hello-robot/stretch_tool_share/tool_share/stretch_RE1_arm/README.md

## Stretch RE1 Arm Model

**Created by**: Hello Robot Inc

This is an STL model of the Stretch RE1 arm (retracted) including the end-of-arm interface. It can assist the design of your own tools for your Stretch. 



| Files                                          |
| ---------------------------------------------- |
| [Stretch_RE1_Arm.STL](CAD/Stretch_RE1_Arm.STL) |
