hello-robot/stretch_tool_share/tool_share/adapted_spoon_V1/images/Spoon.jpeg

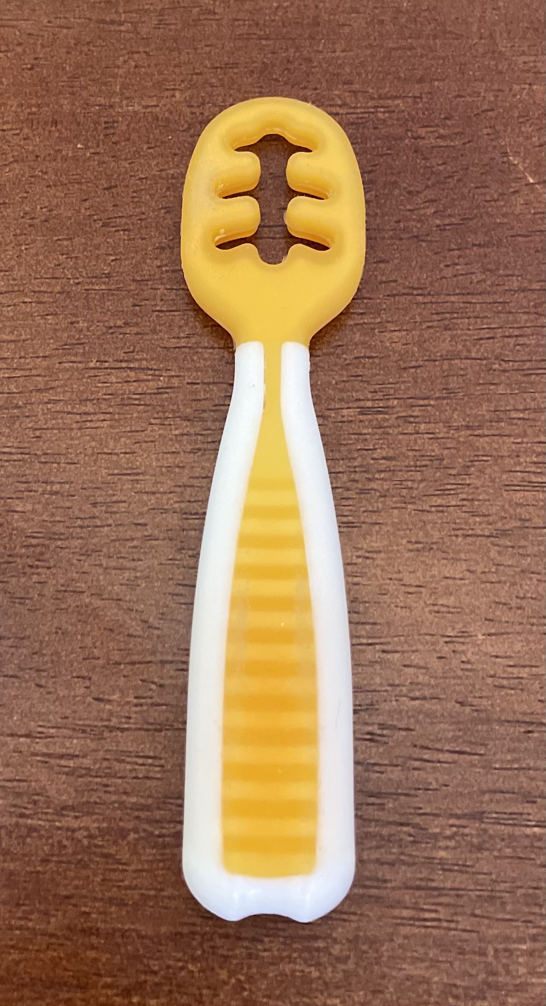
tool_share/adapted_spoon_V1/images/Spoon.jpeg
