hello-robot/stretch_tool_share/tool_share/phone_holder_V1/images/iPhone_Mount_Amazon.PNG

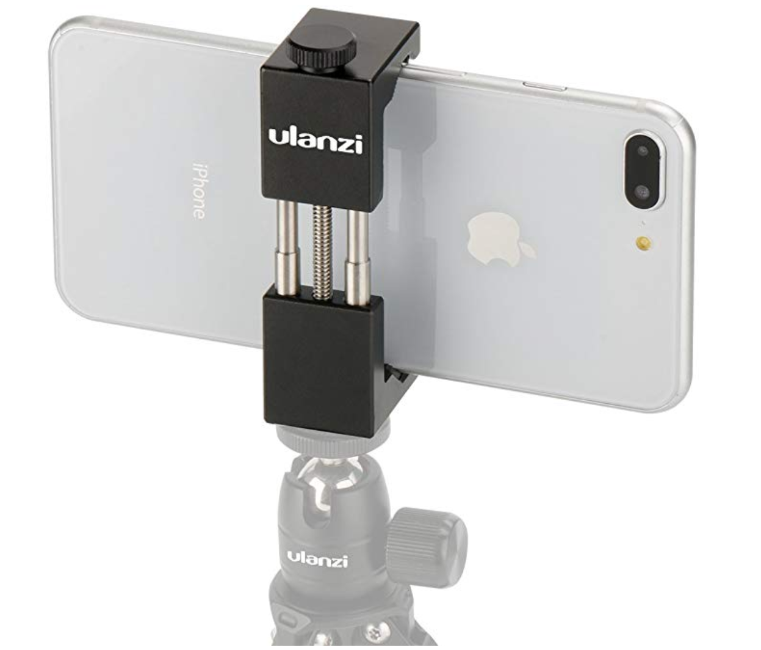
tool_share/phone_holder_V1/images/iPhone_Mount_Amazon.PNG
