hello-robot/stretch_tool_share/tool_share/stretch_teleop_kit/images/camera_view_A.jpg

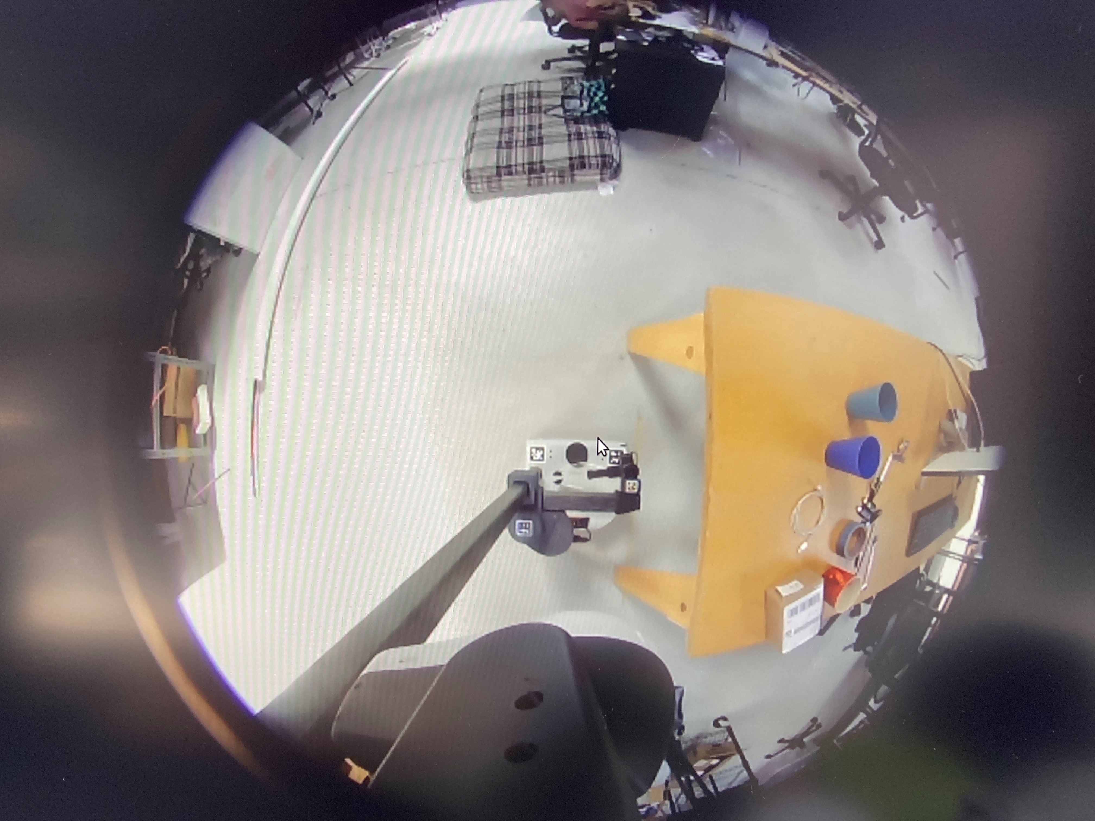
tool_share/stretch_teleop_kit/images/camera_view_A.jpg
