hello-robot/stretch_tool_share/tool_share/stretch_teleop_kit/images/head_camera_A.png

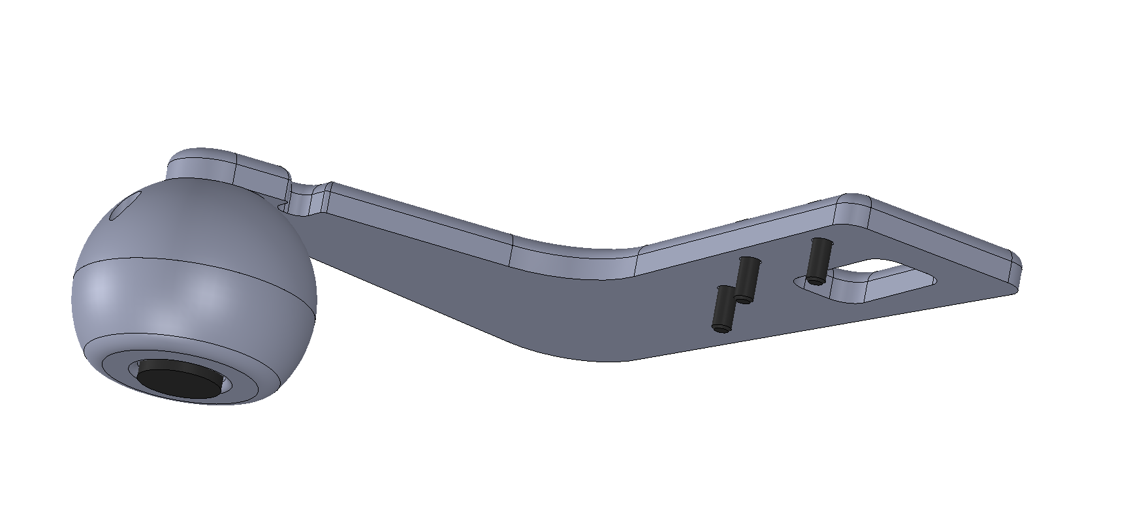
tool_share/stretch_teleop_kit/images/head_camera_A.png
