hello-robot/stretch_tool_share/tool_share/stretch_teleop_kit/images/wrist_camera_C.png

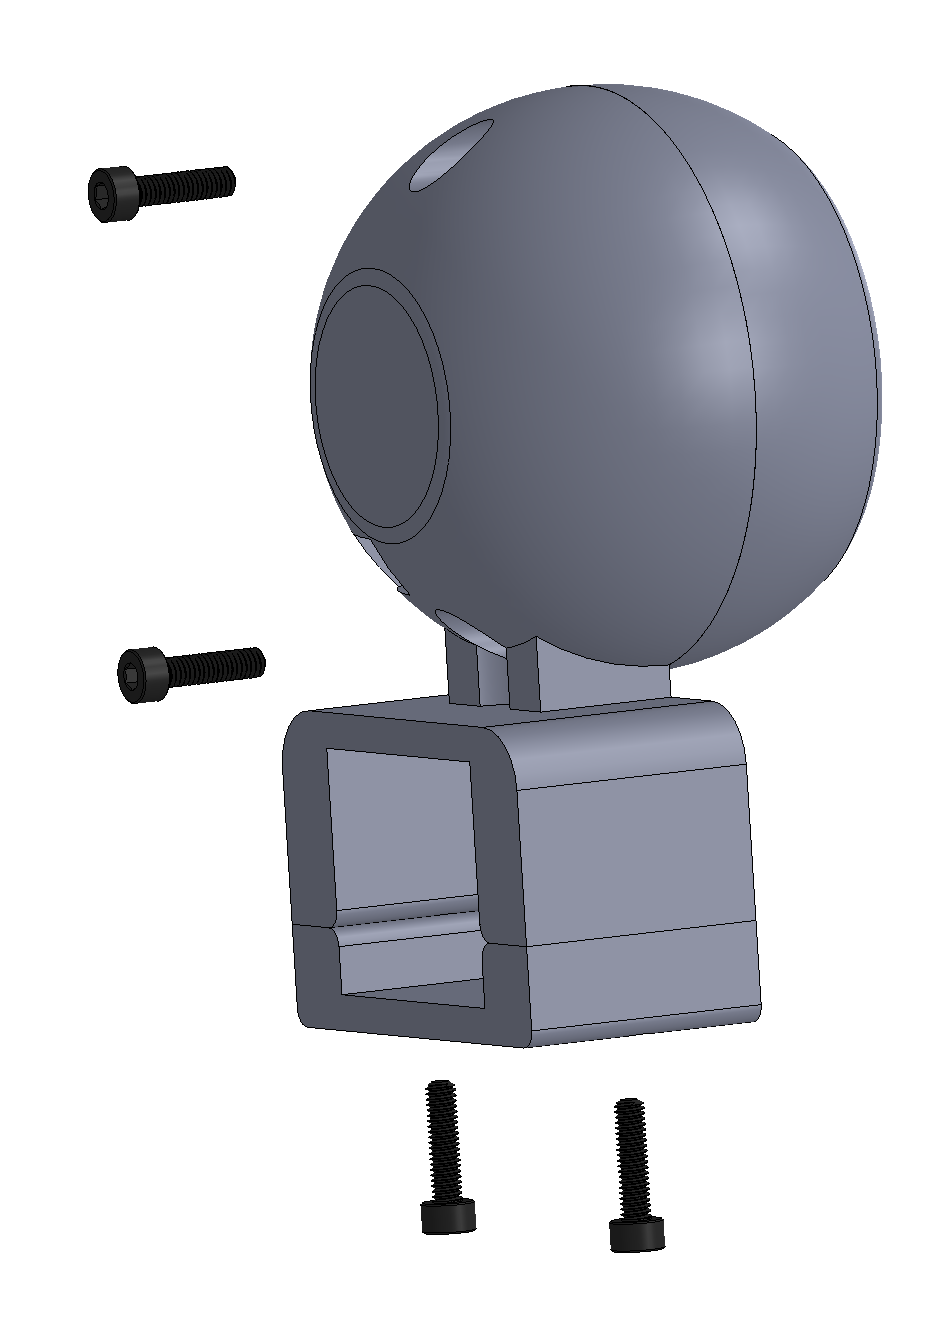
tool_share/stretch_teleop_kit/images/wrist_camera_C.png
