hello-robot/stretch_tool_share/tool_share/swivel_tablet_mount/images/Capture.PNG

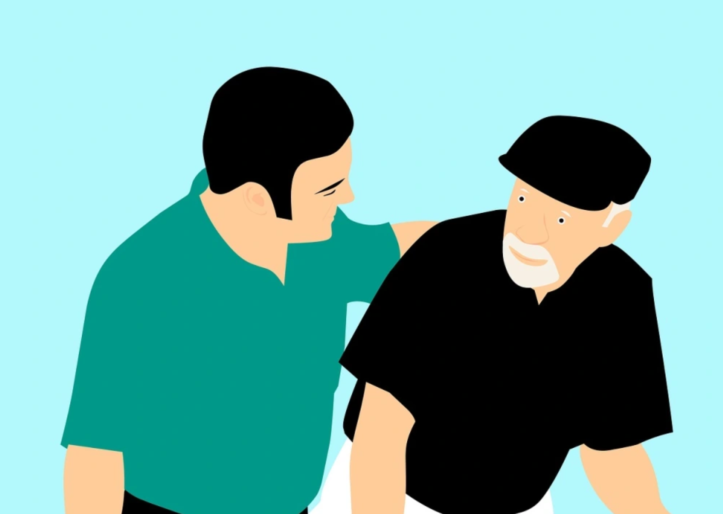
tool_share/swivel_tablet_mount/images/Capture.PNG
