hello-robot/stretch_tool_share/tool_share/stretch_dex_wrist/stretch_description/meshes/link_wrist_roll.STL

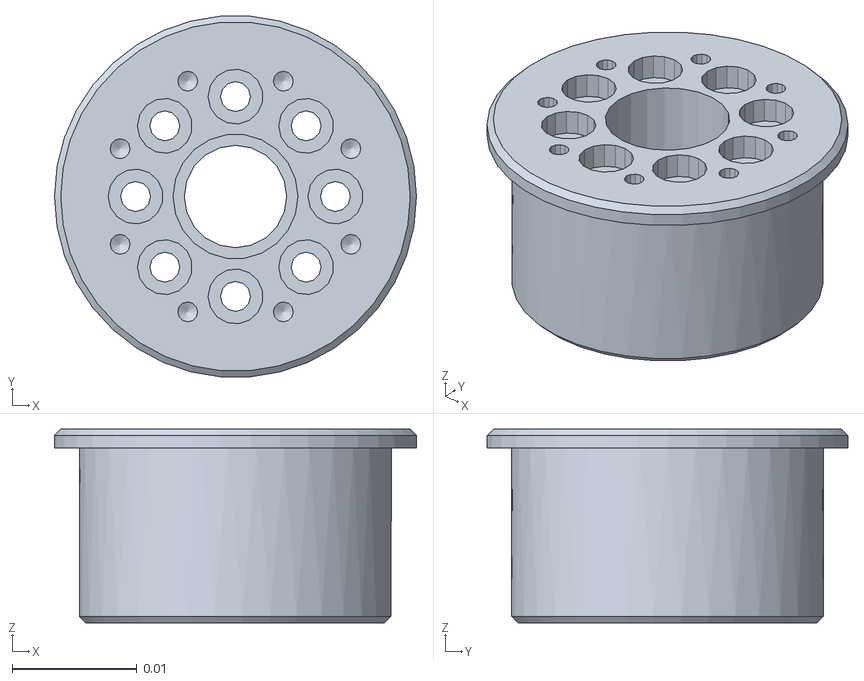
[picture p100: CAD file, 2021-03-02]
tool_share/stretch_dex_wrist/stretch_description/meshes/link_wrist_roll.STL
0.029 x 0.0289 x 0.0155
