hello-robot/stretch_tool_share/tool_share/stretch_docking_station/stretch_docking_station_description/meshes/link_docking_aruco.STL

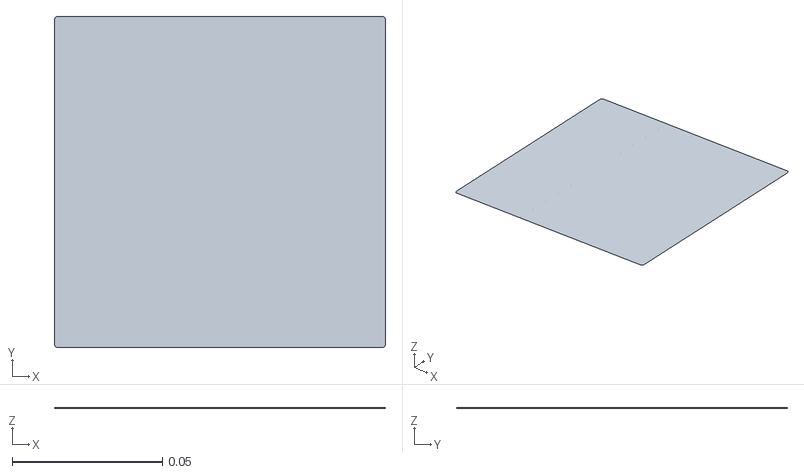
[picture p101: CAD file, 2022-05-09]
tool_share/stretch_docking_station/stretch_docking_station_description/meshes/link_docking_aruco.STL
0.11 x 0.11 x 0.00025
