hello-robot/stretch_tool_share/tool_share/stretch_RE1_arm/CAD/Hello-Robot-Stretch-RE1_Wrist_Module.STEP

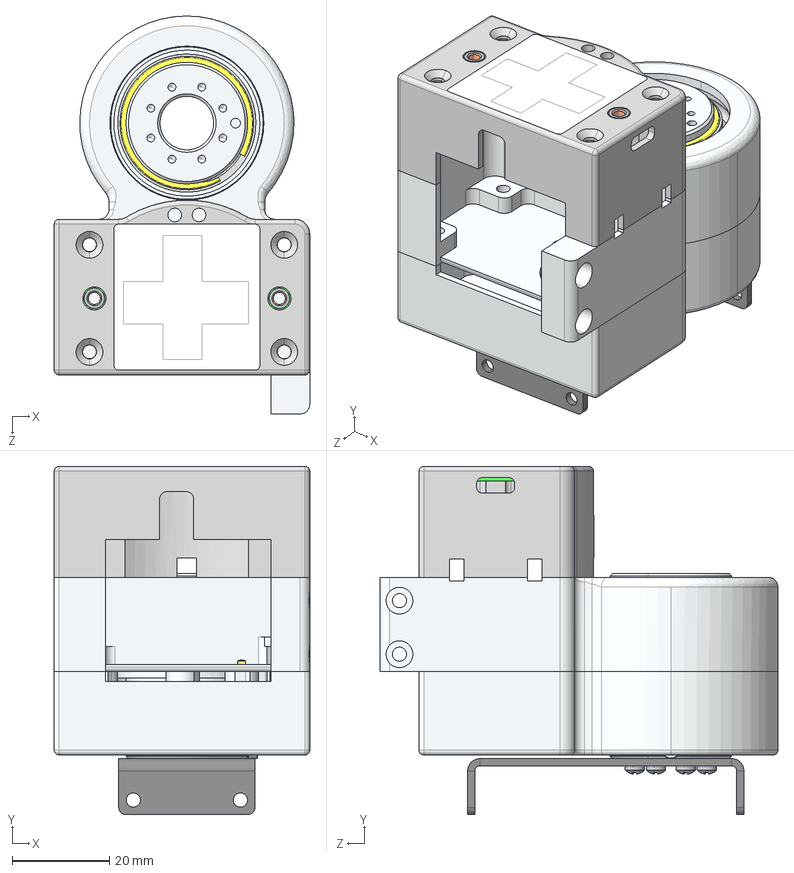
[picture p102: CAD file, 2021-01-28]
tool_share/stretch_RE1_arm/CAD/Hello-Robot-Stretch-RE1_Wrist_Module.STEP
52.5 x 71.5 x 81.8 mm
HDW-609_wrist_output_shaft
HDW-207_91290A012_M2x5mm_SHCS_91290A012
BIG-608_wrist_bearing_block
3DP-239_wrist_bearing_spacer
HDW-209_25x37x7mm_BEARING_5972K216 x 2
VND-278_wrist_top_plate
VND-279_SO-M3-3ZI-PennEngineering x 2
BIG-235_wrist_top_shell
BIG-234_wrist_bottom_shell
HDW-213_94540A360_1in_SPIRAL EXTERNAL RETAINING RING_94540A360
HDW-360_Aruco_E_30x30mm
HDW-359_Aruco_D_30x30mm
HDW-607_gripper_mount_bracket
HDW-362_95836A109_M2x6mm_BHCS_Philips_95836A109 x 8
