hello-robot/stretch_tool_share/tool_share/stretch_RE1_head/CAD/Stretch_RE1_Head_Right.STL

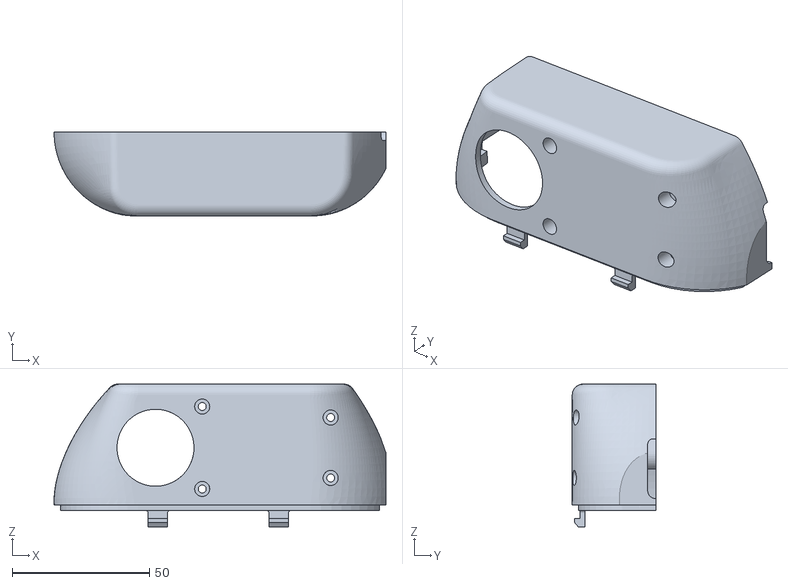
[picture p103: CAD file, 2020-10-14]
tool_share/stretch_RE1_head/CAD/Stretch_RE1_Head_Right.STL
120.8 x 30.5 x 52.0
