hello-robot/stretch_tool_share/tool_share/stretch_shoulder/Shoulder_Mount_CAD.stp

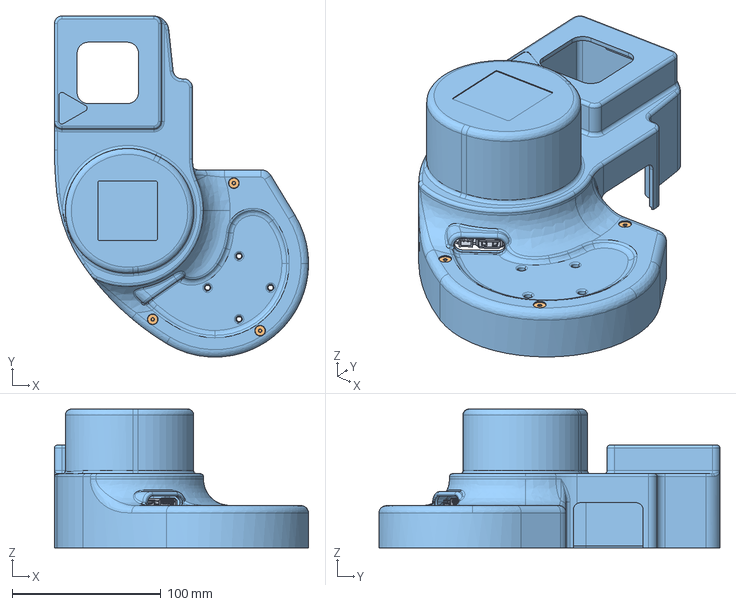
[picture p104: CAD file, 2025-03-24]
tool_share/stretch_shoulder/Shoulder_Mount_CAD.stp
171.0 x 229.5 x 93.5 mm
