hello-robot/stretch_tool_share/tool_share/stretch_teleop_kit/CAD/3DP-809_Head_Teleop_Mount_Back.STL

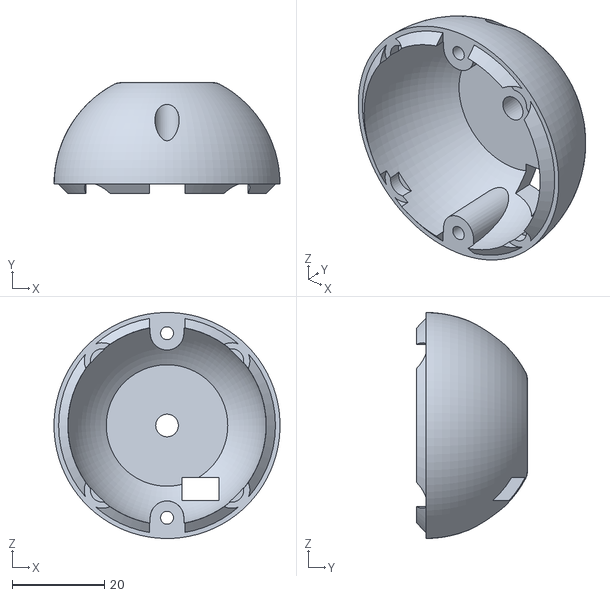
[picture p105: CAD file, 2022-04-29]
tool_share/stretch_teleop_kit/CAD/3DP-809_Head_Teleop_Mount_Back.STL
49.0 x 24.0 x 49.0
