hello-robot/stretch_tool_share/tool_share/stretch_teleop_kit/stretch_description/meshes/link_head_teleop_mount.STL

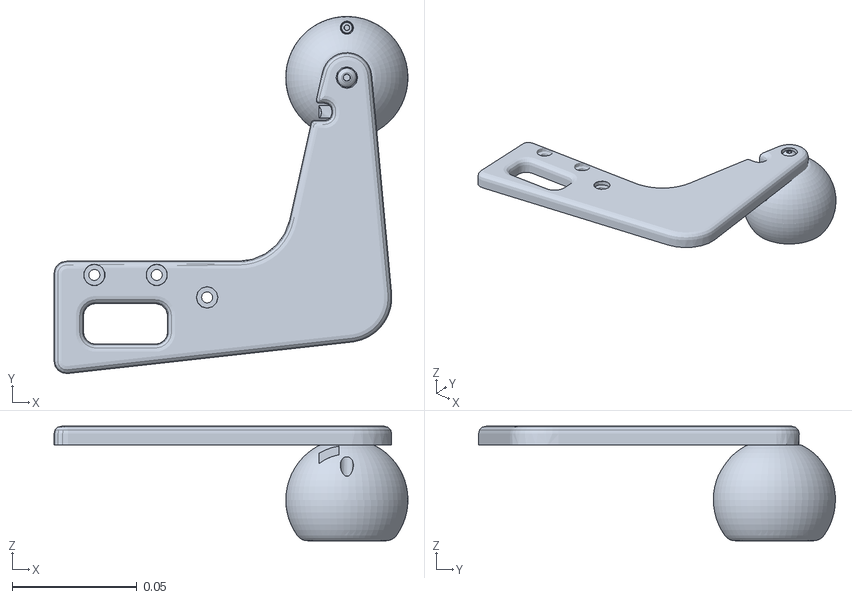
[picture p106: CAD file, 2022-04-28]
tool_share/stretch_teleop_kit/stretch_description/meshes/link_head_teleop_mount.STL
0.142 x 0.143 x 0.0459
