hello-robot/stretch_tool_share/tool_share/swiffer_mount_V1/CAD/swiffer_mount.STL

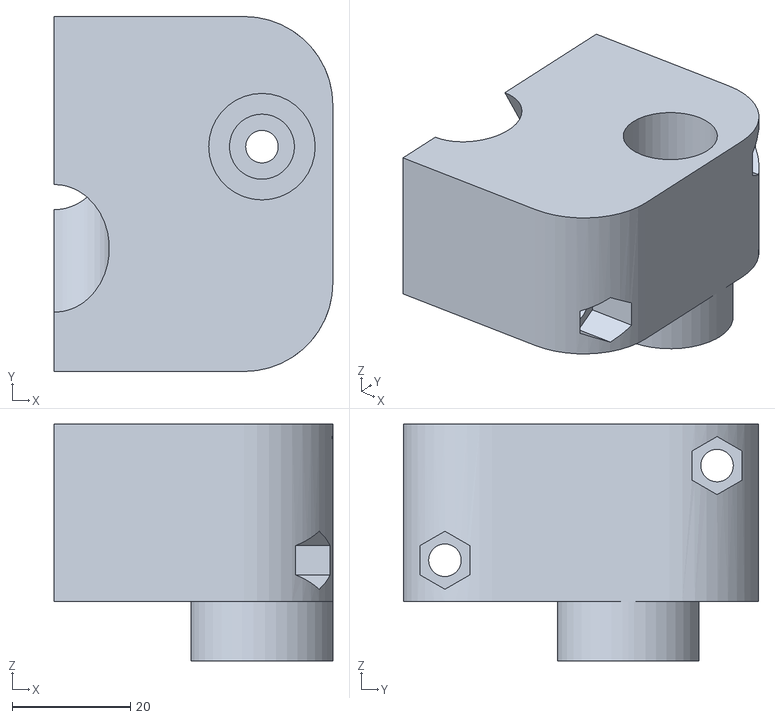
[picture p107: CAD file, 2020-06-18]
tool_share/swiffer_mount_V1/CAD/swiffer_mount.STL
47.1 x 60.0 x 40.0
