hello-robot/stretch_tool_share/tool_share/swivel_tablet_mount/CAD/swivel_adapter_top.STL

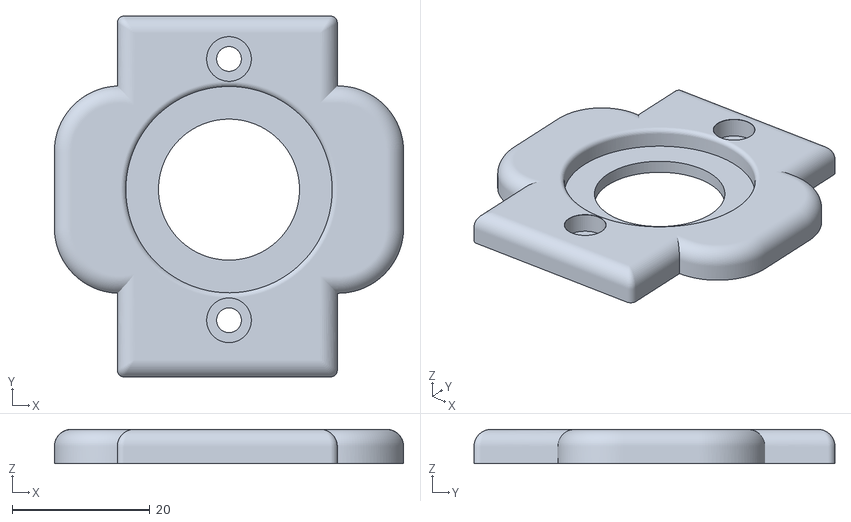
[picture p108: CAD file, 2023-11-14]
tool_share/swivel_tablet_mount/CAD/swivel_adapter_top.STL
50.8 x 52.5 x 5.00
