hello-robot/stretch_tool_share/tool_share/tray_cup_holder_V1/CAD/ASSEM_tray_cupholder_V1.STL

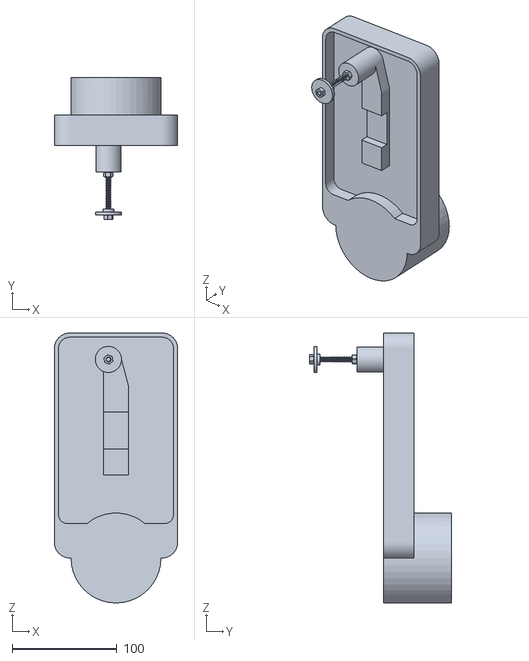
[picture p109: CAD file, 2020-06-18]
tool_share/tray_cup_holder_V1/CAD/ASSEM_tray_cupholder_V1.STL
118.0 x 136.2 x 258.0
