hello-robot/stretch_tool_share/tool_share/wrist_USB_board_camera/CAD/Board_Camera_Ball_Cover.STL

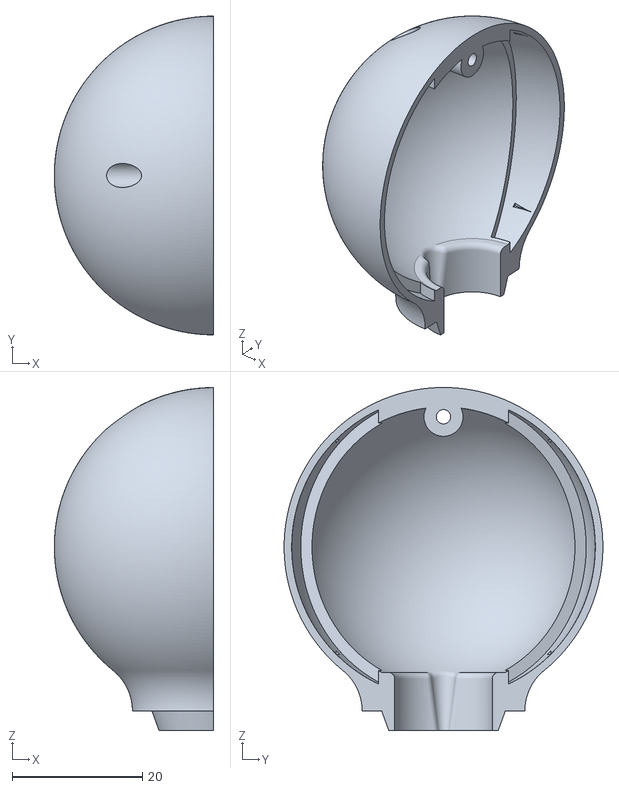
[picture p110: CAD file, 2023-03-30]
tool_share/wrist_USB_board_camera/CAD/Board_Camera_Ball_Cover.STL
24.5 x 49.0 x 52.7
