hello-robot/stretch_tool_share/tool_share/wrist_USB_board_camera/stretch_description/meshes/link_wrist_USB_board_camera.STL

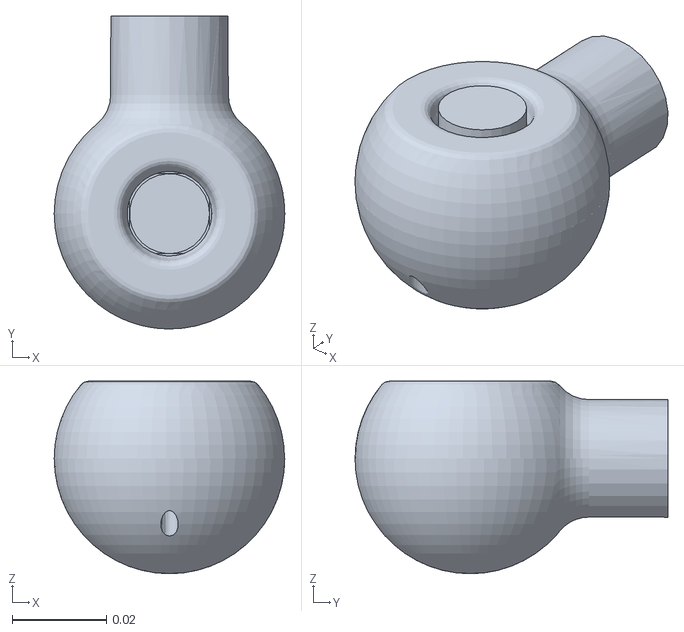
[picture p111: CAD file, 2021-02-11]
tool_share/wrist_USB_board_camera/stretch_description/meshes/link_wrist_USB_board_camera.STL
0.049 x 0.0665 x 0.0409
