hello-robot/stretch_tool_share/tool_share_SE3/eoa_wrist_dw3_tool_tablet_12in/CAD/DW3_tablet_holder.STEP

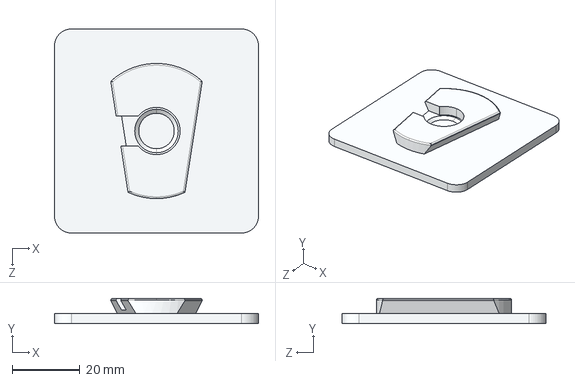
[picture p112: CAD file, 2024-01-28]
tool_share_SE3/eoa_wrist_dw3_tool_tablet_12in/CAD/DW3_tablet_holder.STEP
60.3 x 7.40 x 60.3 mm
