hello-robot/stretch_tool_share/tool_share_SE3/eoa_wrist_dw3_tool_tablet_12in/meshes/link_DW3_tablet_12in.STL

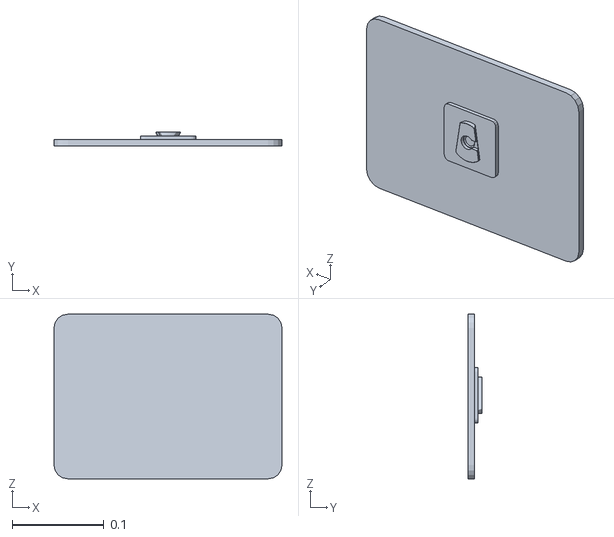
[picture p113: CAD file, 2024-01-28]
tool_share_SE3/eoa_wrist_dw3_tool_tablet_12in/meshes/link_DW3_tablet_12in.STL
0.249 x 0.0152 x 0.179
