hello-robot/stretch_tool_share/tool_share/card_holder_V1.5/CAD/base_v2.STL

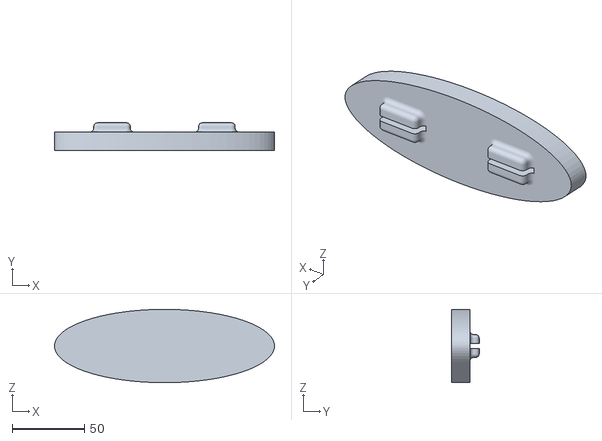
[picture p114: CAD file, 2022-08-03]
tool_share/card_holder_V1.5/CAD/base_v2.STL
152.4 x 19.1 x 50.8
