hello-robot/stretch_tool_share/tool_share/dry_erase_holder_V1/CAD/dry_erase_bushing_block.STL

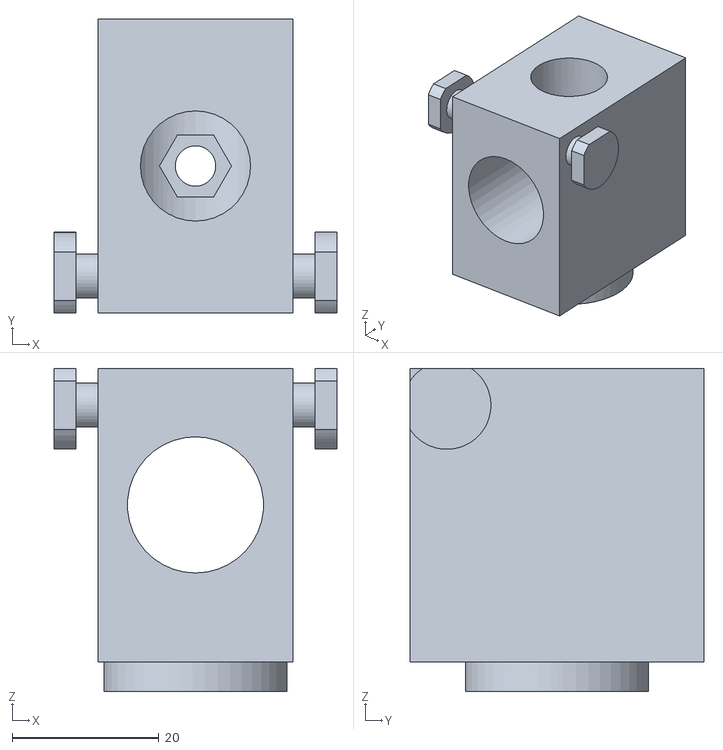
[picture p115: CAD file, 2020-06-18]
tool_share/dry_erase_holder_V1/CAD/dry_erase_bushing_block.STL
38.5 x 40.0 x 44.0
