hello-robot/stretch_tool_share/tool_share/dry_erase_holder_V1/stretch_description/meshes/link_dry_erase_marker.STL

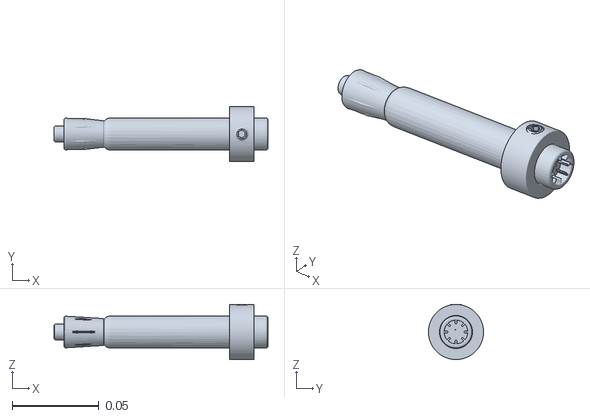
[picture p116: CAD file, 2021-02-11]
tool_share/dry_erase_holder_V1/stretch_description/meshes/link_dry_erase_marker.STL
0.123 x 0.0317 x 0.0318
