hello-robot/stretch_tool_share/tool_share/puller_v1/CAD/Puller_V1.STL

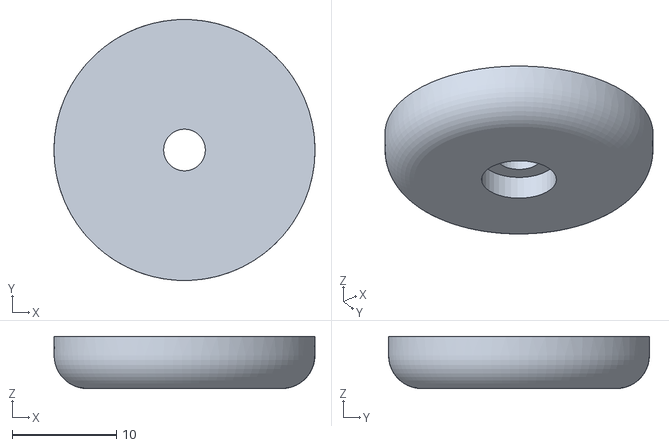
[picture p117: CAD file, 2020-06-18]
tool_share/puller_v1/CAD/Puller_V1.STL
25.0 x 25.0 x 5.00
