hello-robot/stretch_tool_share/tool_share/stretch_2_STEP/CAD/SIM-401_Roll_Hanger_simple.STEP

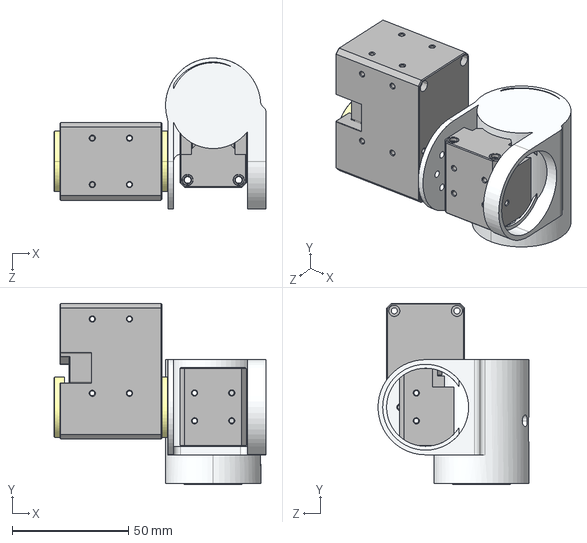
[picture p118: CAD file, 2023-01-04]
tool_share/stretch_2_STEP/CAD/SIM-401_Roll_Hanger_simple.STEP
91.3 x 78.1 x 65.0 mm
