hello-robot/stretch_tool_share/tool_share/stretch_dex_wrist/stretch_description/meshes/link_wrist_pitch.STL

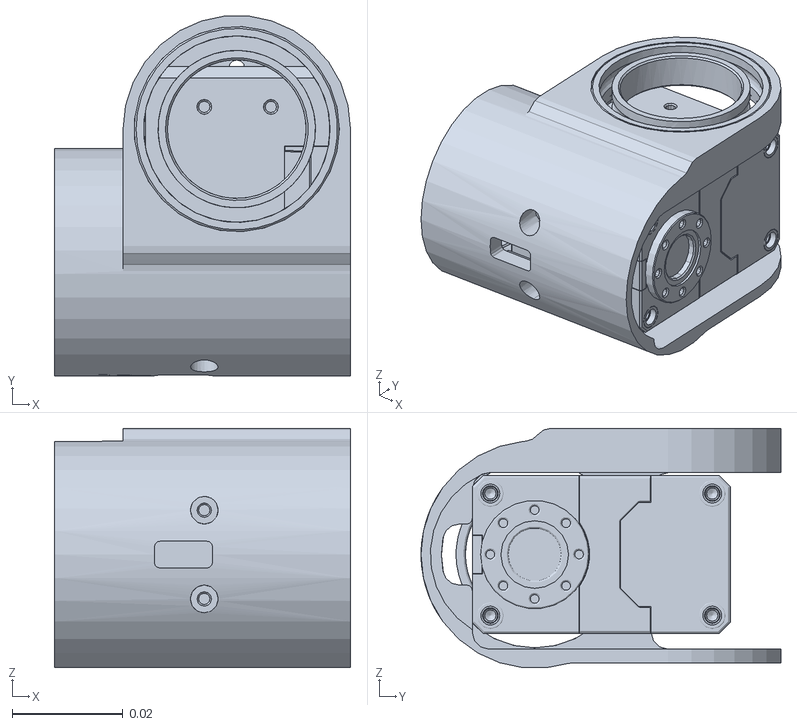
[picture p119: CAD file, 2021-02-24]
tool_share/stretch_dex_wrist/stretch_description/meshes/link_wrist_pitch.STL
0.0534 x 0.0649 x 0.0431
