hello-robot/stretch_tool_share/tool_share/stretch_RE1_arm/CAD/Stretch_RE1_Arm.STL

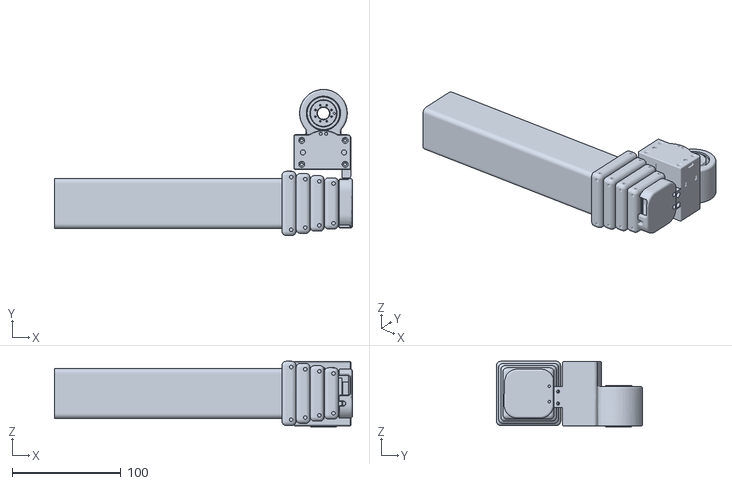
[picture p120: CAD file, 2020-06-18]
tool_share/stretch_RE1_arm/CAD/Stretch_RE1_Arm.STL
274.5 x 134.6 x 60.4
