hello-robot/stretch_tool_share/tool_share/stretch_teleop_kit/CAD/3DP-808_Teleop_Camera_Mount_Front.STL

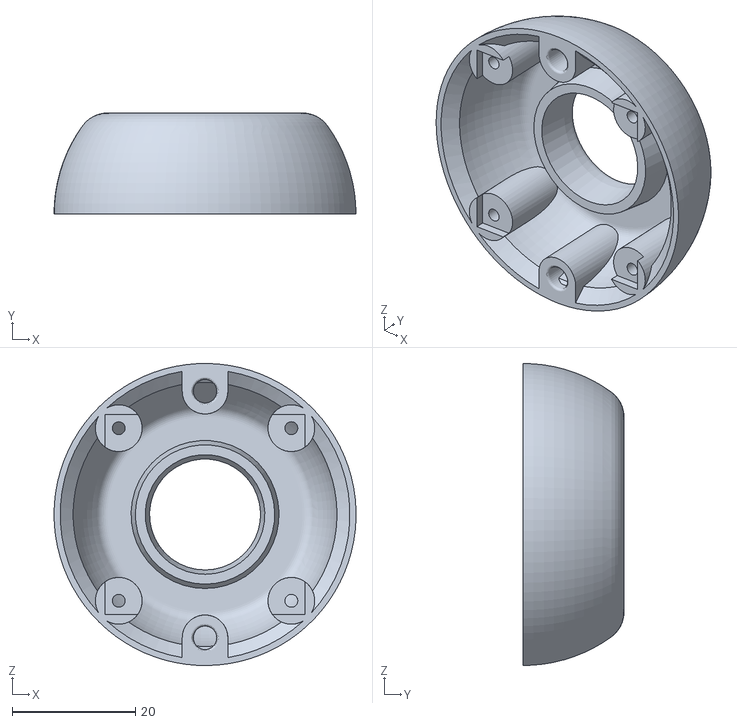
[picture p121: CAD file, 2022-04-29]
tool_share/stretch_teleop_kit/CAD/3DP-808_Teleop_Camera_Mount_Front.STL
49.0 x 16.4 x 49.0
