hello-robot/stretch_tool_share/tool_share/stretch_teleop_kit/stretch_description/meshes/link_head_teleop_camera.STL

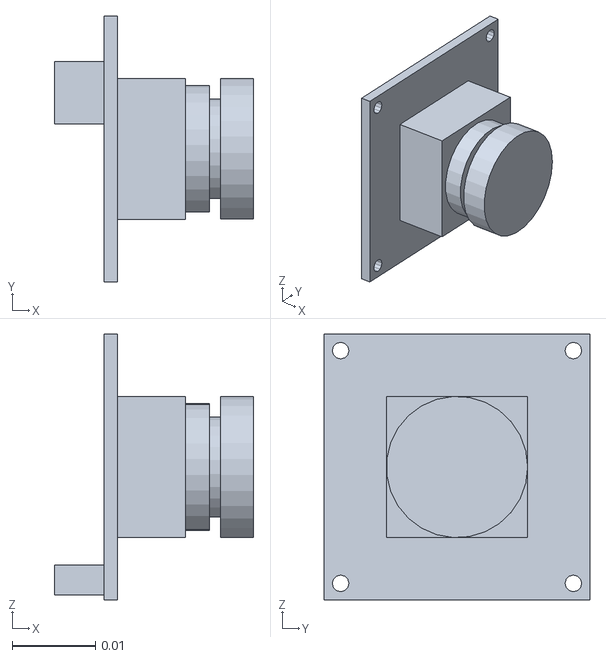
[picture p122: CAD file, 2022-04-28]
tool_share/stretch_teleop_kit/stretch_description/meshes/link_head_teleop_camera.STL
0.024 x 0.032 x 0.032
