hello-robot/stretch_tool_share/tool_share/swiffer_mount_V1/CAD/swiffer_mount_clamp.STL

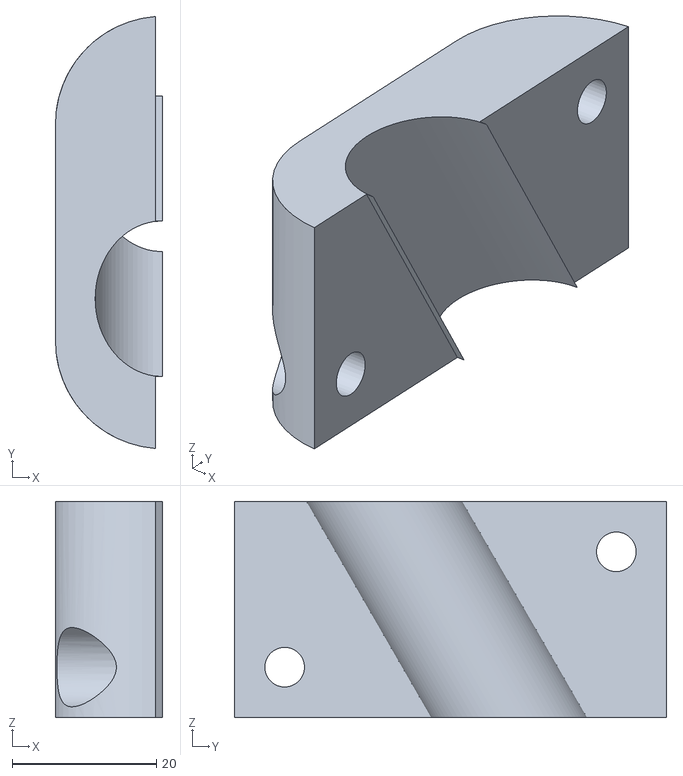
[picture p123: CAD file, 2020-06-18]
tool_share/swiffer_mount_V1/CAD/swiffer_mount_clamp.STL
14.9 x 59.9 x 30.0
