hello-robot/stretch_tool_share/tool_share/wrist_USB_board_camera/CAD/Spinel_camera_wide_fov.STL

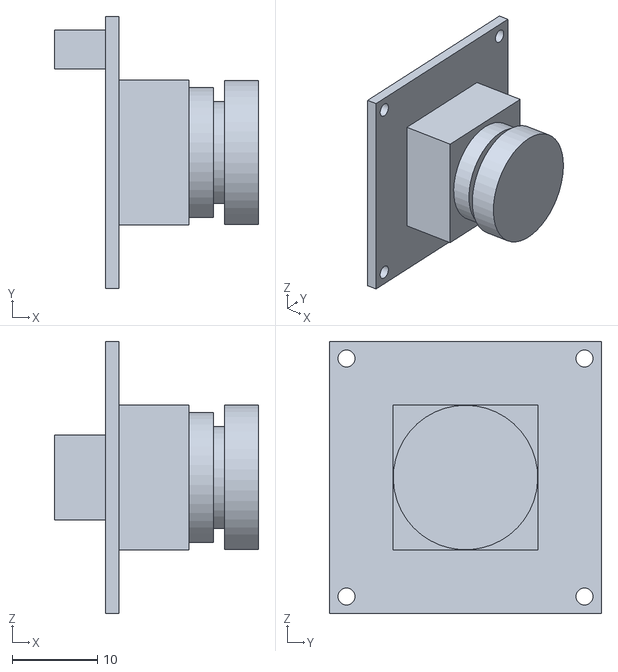
[picture p125: CAD file, 2021-02-11]
tool_share/wrist_USB_board_camera/CAD/Spinel_camera_wide_fov.STL
24.0 x 32.0 x 32.0
