hello-robot/stretch_tool_share/tool_share_SE3/eoa_wrist_dw3_tool_tablet_12in/meshes/link_DW3_tablet_12in_collision.STL

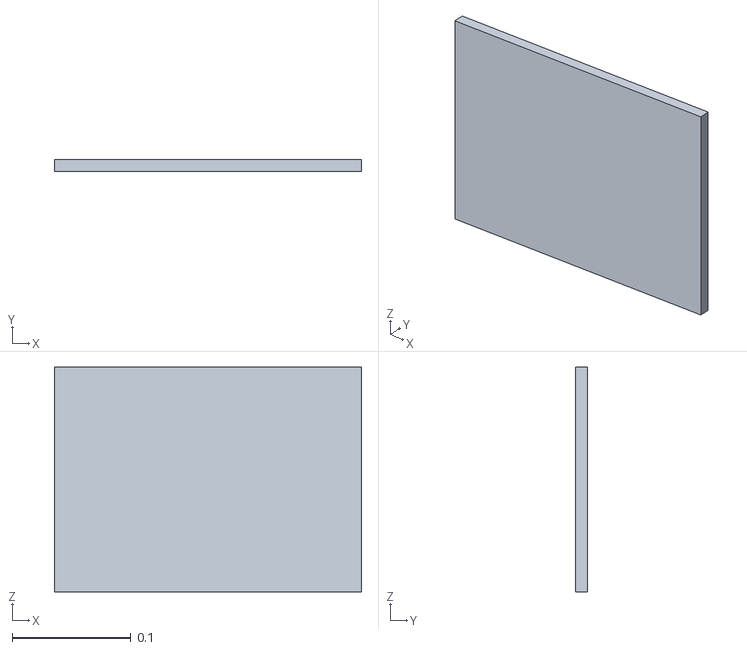
[picture p126: CAD file, 2024-01-28]
tool_share_SE3/eoa_wrist_dw3_tool_tablet_12in/meshes/link_DW3_tablet_12in_collision.STL
0.259 x 0.01 x 0.19
