hello-robot/stretch_tool_share/tool_share/card_holder_V1.5/CAD/pull_tab.STL

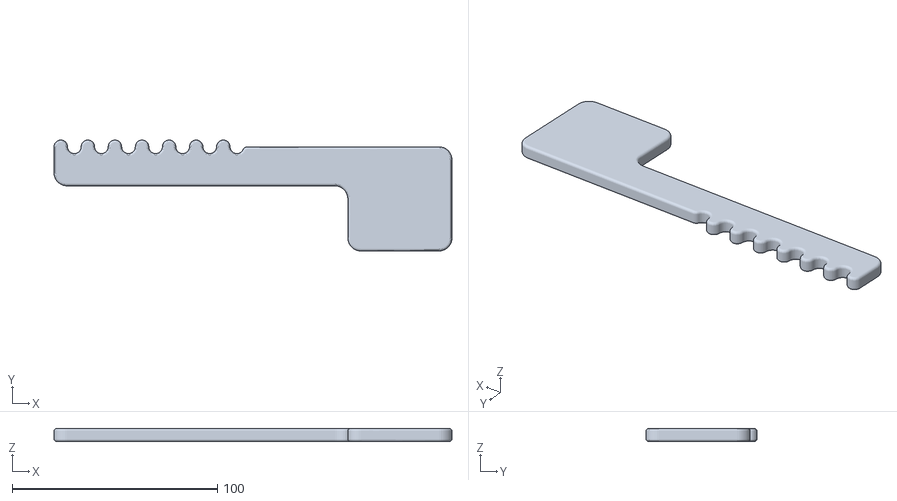
[picture p127: CAD file, 2022-08-03]
tool_share/card_holder_V1.5/CAD/pull_tab.STL
194.1 x 54.1 x 6.35
