hello-robot/stretch_tool_share/tool_share/stretch_2_STEP/CAD/SUB-216_Dex_Wrist_simple.STEP

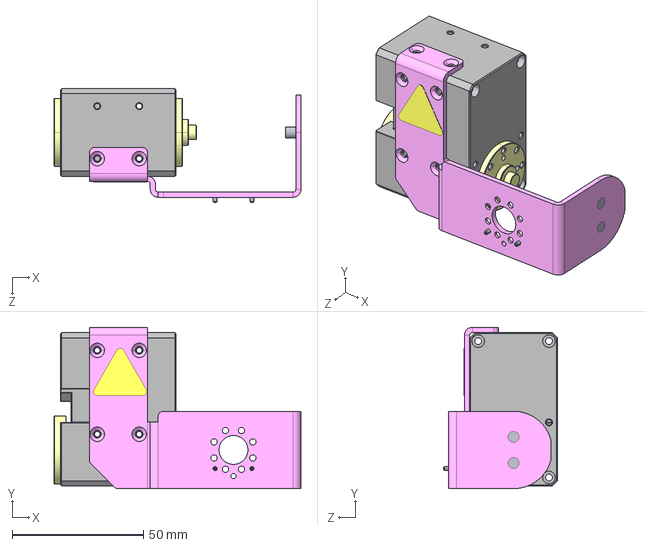
[picture p128: CAD file, 2023-01-04]
tool_share/stretch_2_STEP/CAD/SUB-216_Dex_Wrist_simple.STEP
94.2 x 61.5 x 43.5 mm
