hello-robot/stretch_tool_share/tool_share/stretch_dex_wrist/stretch_description/meshes/link_wrist_yaw_bottom.STL

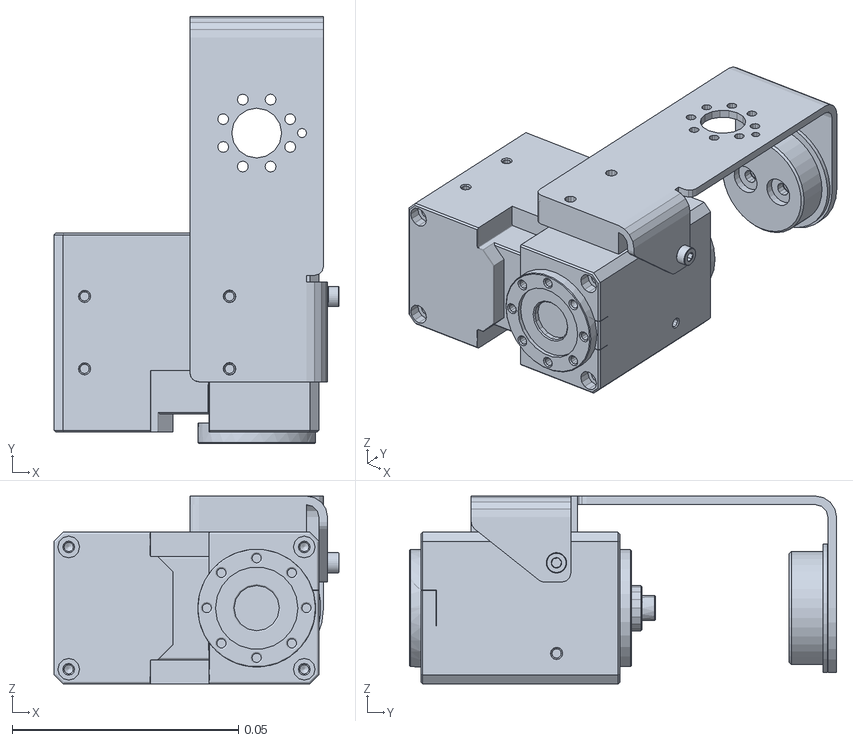
[picture p129: CAD file, 2021-02-24]
tool_share/stretch_dex_wrist/stretch_description/meshes/link_wrist_yaw_bottom.STL
0.0629 x 0.0943 x 0.0415
