hello-robot/stretch_tool_share/tool_share/stretch_RE1_head/CAD/Stretch_RE1_Head_Camera.STL

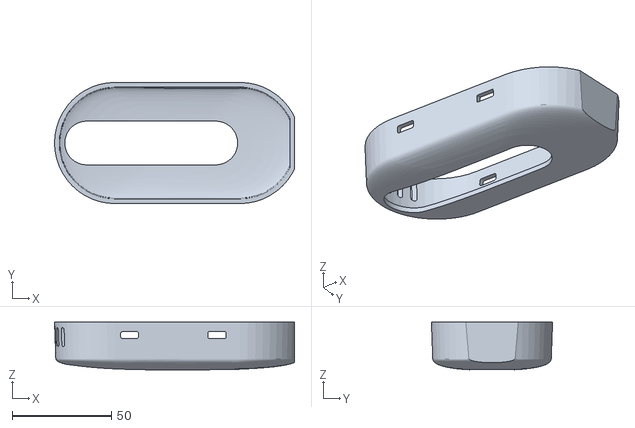
[picture p130: CAD file, 2020-10-14]
tool_share/stretch_RE1_head/CAD/Stretch_RE1_Head_Camera.STL
120.8 x 61.0 x 24.0
