hello-robot/stretch_tool_share/tool_share/stretch_teleop_kit/CAD/3DP-810_Head_Teleop_Mount.STL

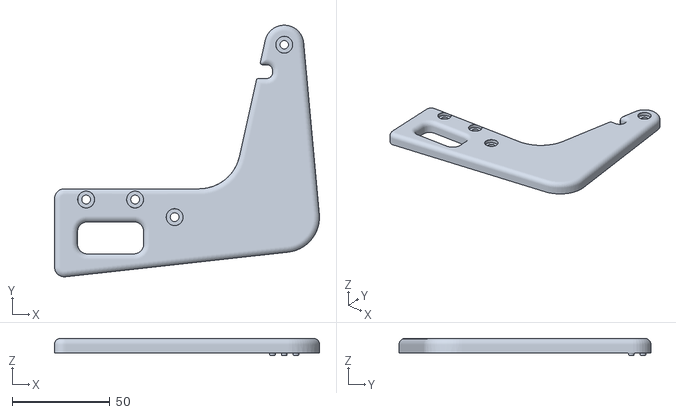
[picture p131: CAD file, 2022-04-29]
tool_share/stretch_teleop_kit/CAD/3DP-810_Head_Teleop_Mount.STL
135.4 x 128.6 x 8.75
