hello-robot/stretch_tool_share/tool_share/swivel_tablet_mount/CAD/tablet_tape_adapter.STL

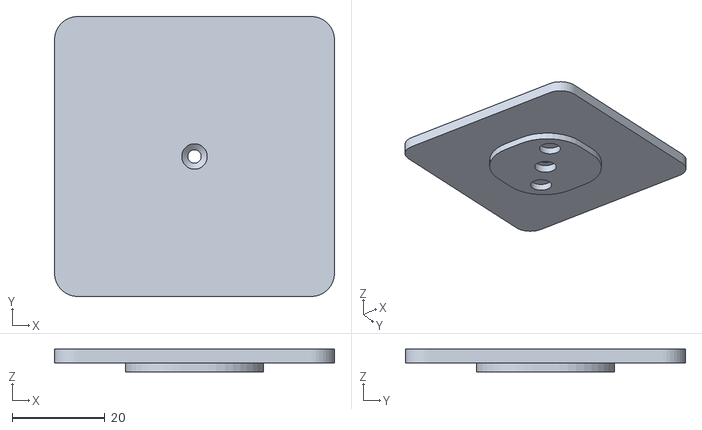
[picture p132: CAD file, 2023-04-05]
tool_share/swivel_tablet_mount/CAD/tablet_tape_adapter.STL
60.3 x 60.3 x 4.90
