hello-robot/stretch_tool_share/tool_share/tray_cup_holder_V1/CAD/tray_clip.STL

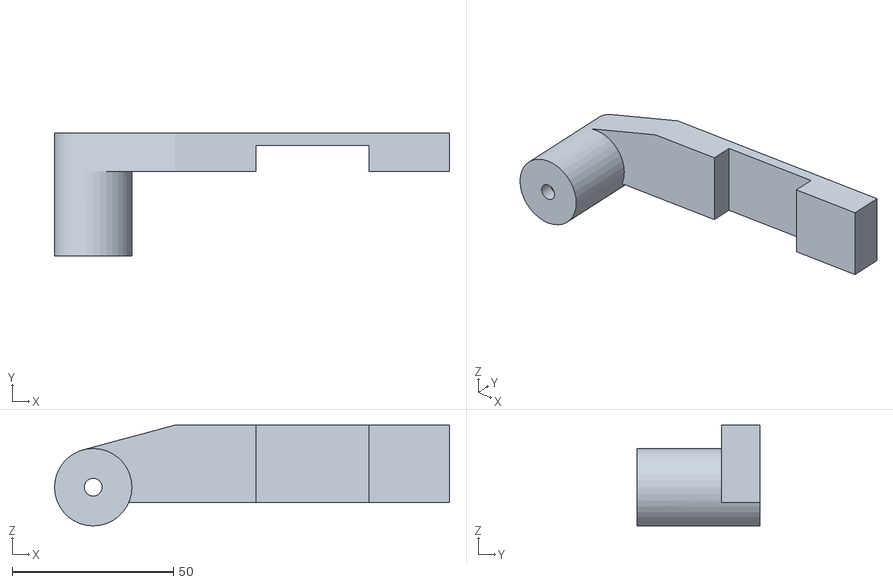
[picture p133: CAD file, 2020-06-18]
tool_share/tray_cup_holder_V1/CAD/tray_clip.STL
122.4 x 38.2 x 31.2
