hello-robot/stretch_tool_share/tool_share/card_holder_V1.5/CAD/A_frame.STL

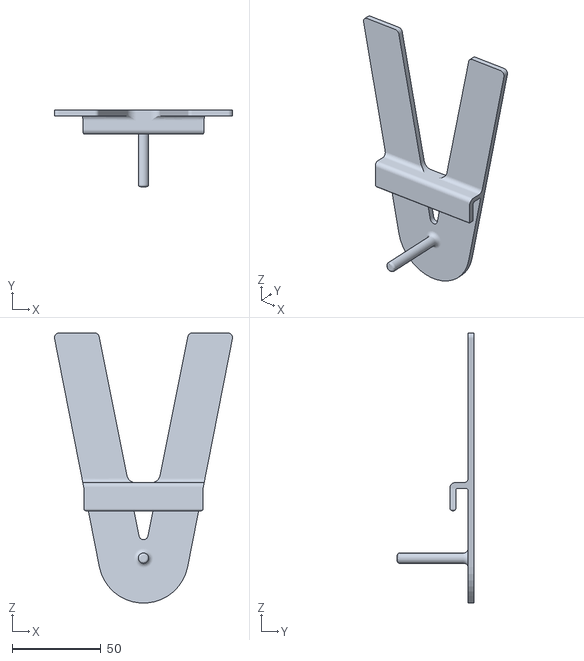
[picture p134: CAD file, 2022-08-03]
tool_share/card_holder_V1.5/CAD/A_frame.STL
100.5 x 43.2 x 152.3
