hello-robot/stretch_tool_share/tool_share/stretch_2_STEP/CAD/HDW-911_gripper_mount_bracket.STEP

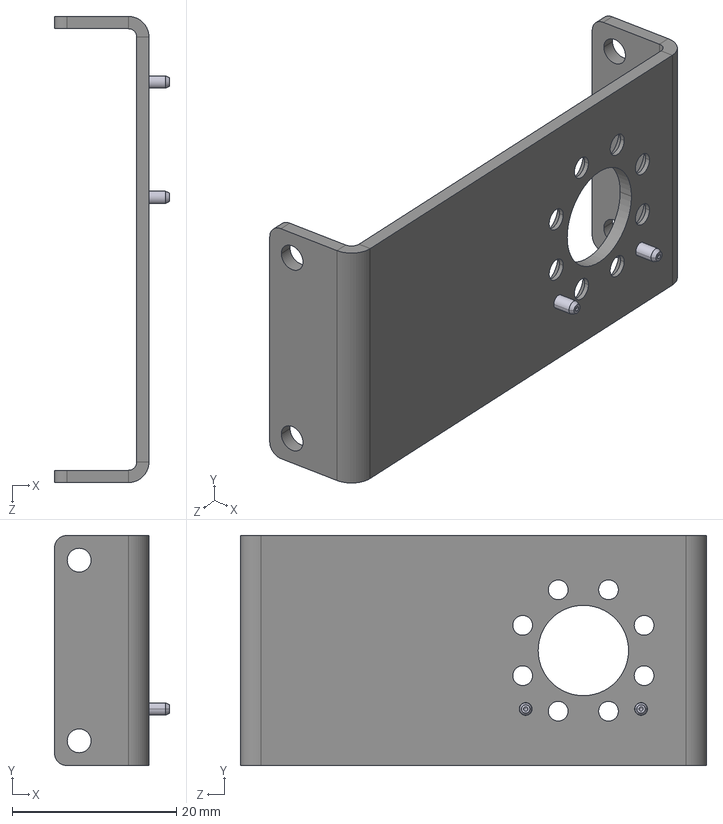
[picture p135: CAD file, 2023-01-04]
tool_share/stretch_2_STEP/CAD/HDW-911_gripper_mount_bracket.STEP
14.0 x 28.0 x 56.7 mm
VND-817_gripper_mount_bracket
VND-818_MPP-1.5mm-4-PennEngineering x 2
