hello-robot/stretch_tool_share/tool_share/stretch_teleop_kit/stretch_description/meshes/link_gripper_teleop_mount.STL

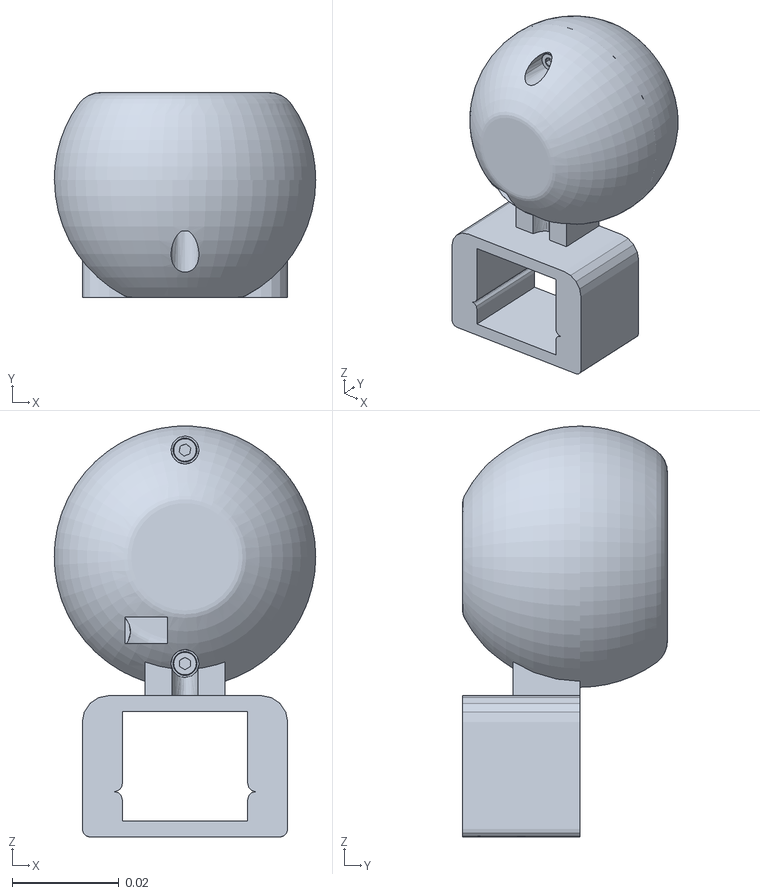
[picture p137: CAD file, 2022-04-28]
tool_share/stretch_teleop_kit/stretch_description/meshes/link_gripper_teleop_mount.STL
0.049 x 0.0384 x 0.077
