hello-robot/stretch_tool_share/tool_share/stretch_teleop_kit/CAD/3DP-812_Gripper_Teleop_Mount_Bottom.STL

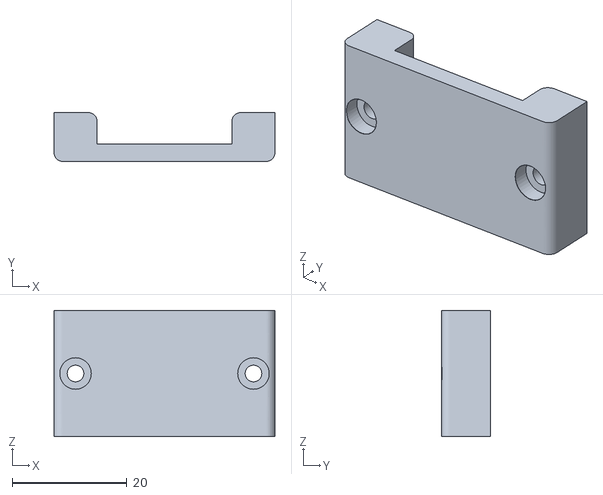
[picture p138: CAD file, 2022-04-29]
tool_share/stretch_teleop_kit/CAD/3DP-812_Gripper_Teleop_Mount_Bottom.STL
38.5 x 8.50 x 22.0
