hello-robot/stretch_tool_share/tool_share/stretch_2_STEP/CAD/SUB-202_head_tilt_simple.STEP

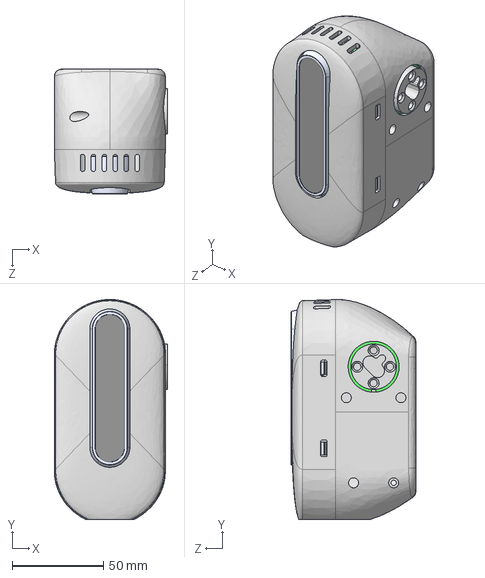
[picture p139: CAD file, 2023-01-04]
tool_share/stretch_2_STEP/CAD/SUB-202_head_tilt_simple.STEP
62.3 x 120.8 x 68.5 mm
